ke0ff/IC900_DUClone/3D/stl/IC901F_back2.stl

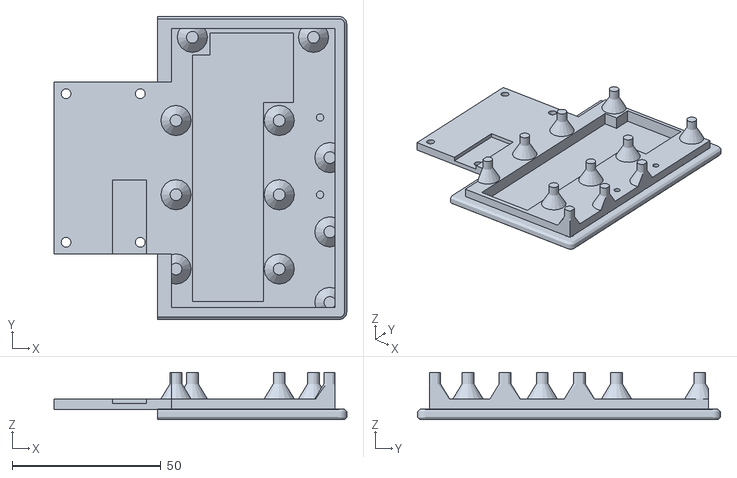
[picture p27: CAD file, 2024-02-04]
3D/stl/IC901F_back2.stl
98.5 x 102.0 x 15.9
