ke0ff/IC900_DUClone/3D/stl/IC901F_sundome.stl

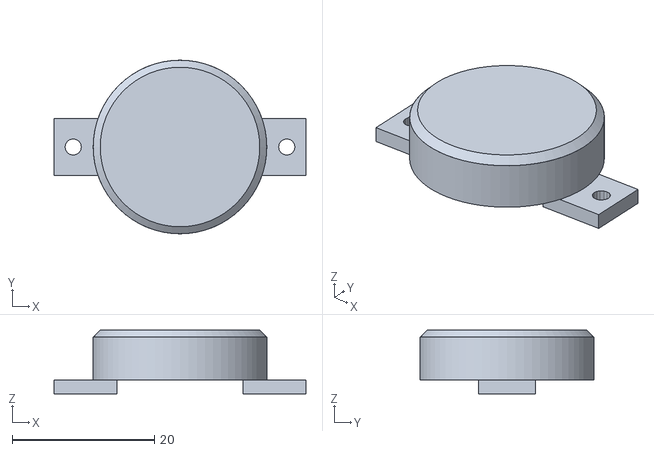
[picture p28: CAD file, 2024-02-04]
3D/stl/IC901F_sundome.stl
35.4 x 24.4 x 8.99
