ke0ff/IC900_DUClone/3D/stl/IC901F_back1.stl

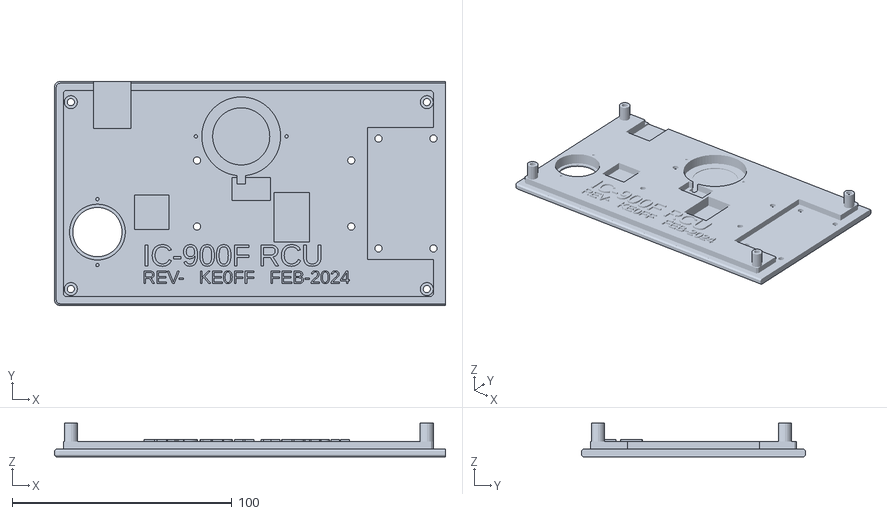
[picture p29: CAD file, 2024-02-04]
3D/stl/IC901F_back1.stl
178.0 x 102.0 x 15.3
