ke0ff/IC900_DUClone/3D/stl/IC901F_dialwin.stl

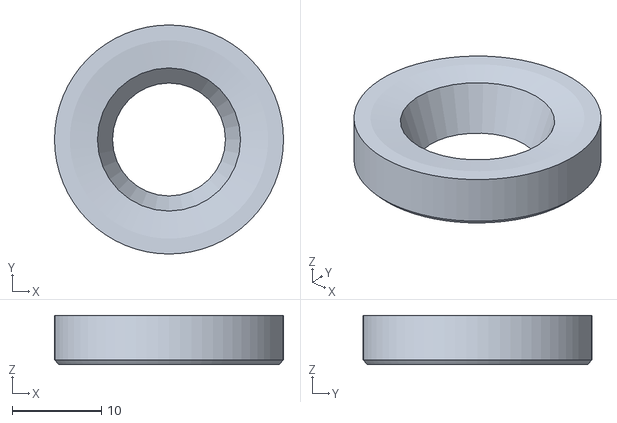
[picture p30: CAD file, 2024-02-04]
3D/stl/IC901F_dialwin.stl
25.7 x 25.7 x 5.50
