ke0ff/IC900_DUClone/3D/stl/IC901F_pot.stl

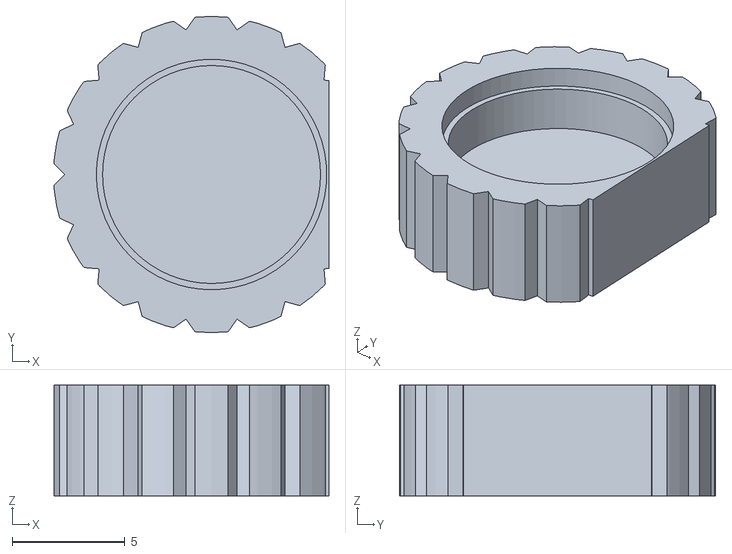
[picture p31: CAD file, 2024-02-04]
3D/stl/IC901F_pot.stl
12.2 x 14.0 x 4.90
