ke0ff/IC900_DUClone/3D/stl/IC900F_vqcap.stl

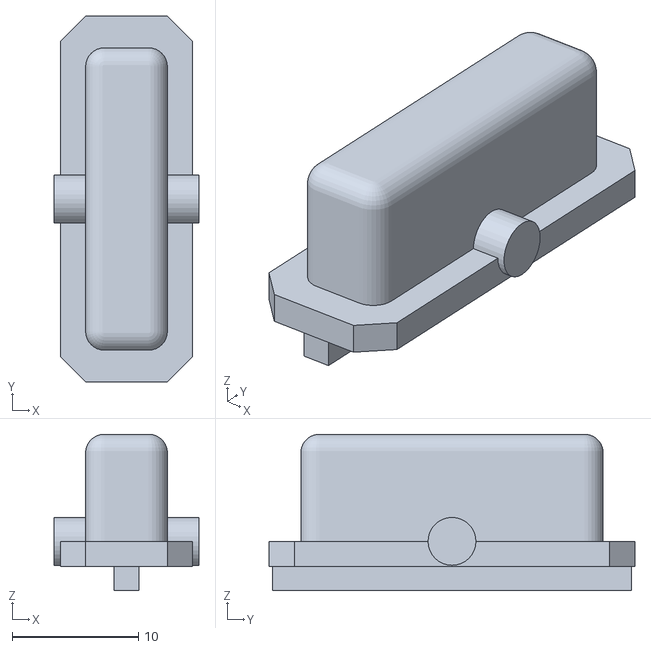
[picture p32: CAD file, 2024-01-06]
3D/stl/IC900F_vqcap.stl
11.5 x 29.0 x 12.4
