ke0ff/IC900_DUClone/3D/stl/LCDpcb.stl

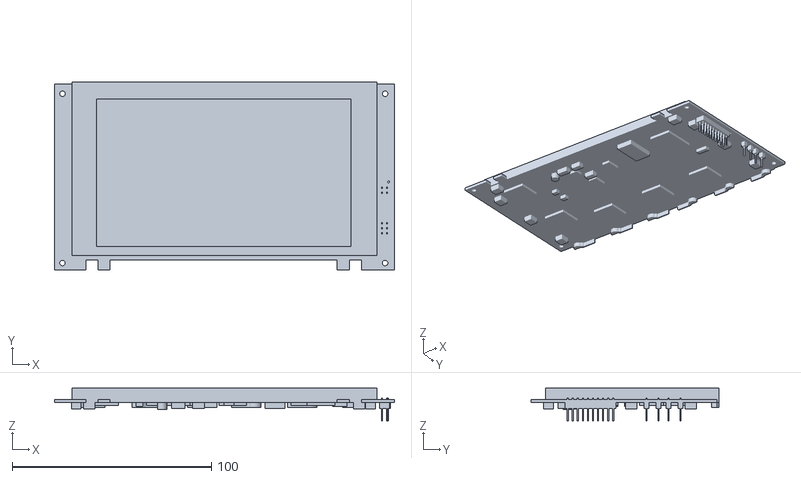
[picture p33: CAD file, 2024-01-06]
3D/stl/LCDpcb.stl
170.5 x 94.5 x 16.4
