ke0ff/IC900_DUClone/3D/stl/IC900F_spacer.stl

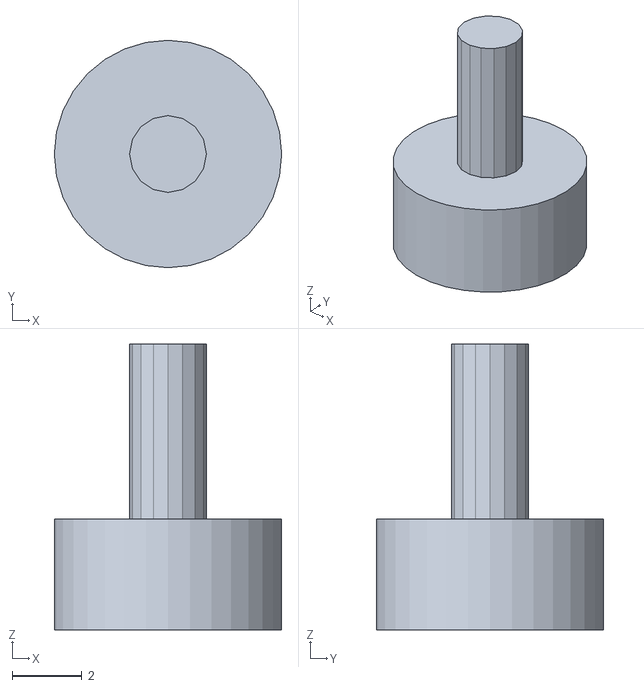
[picture p34: CAD file, 2024-01-06]
3D/stl/IC900F_spacer.stl
6.50 x 6.50 x 8.18
