ke0ff/IC900_DUClone/3D/stl/IC900F_pcb.stl

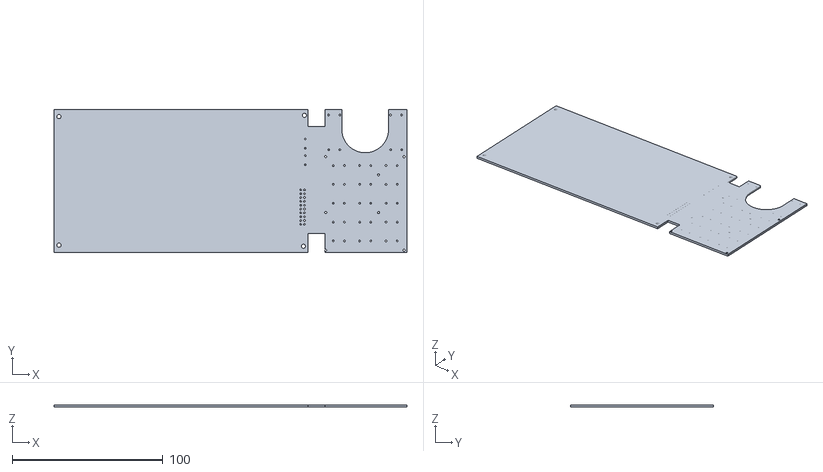
[picture p36: CAD file, 2024-01-06]
3D/stl/IC900F_pcb.stl
234.0 x 94.5 x 1.60
