ke0ff/IC900_DUClone/3D/stl/IC900F_bcap.stl

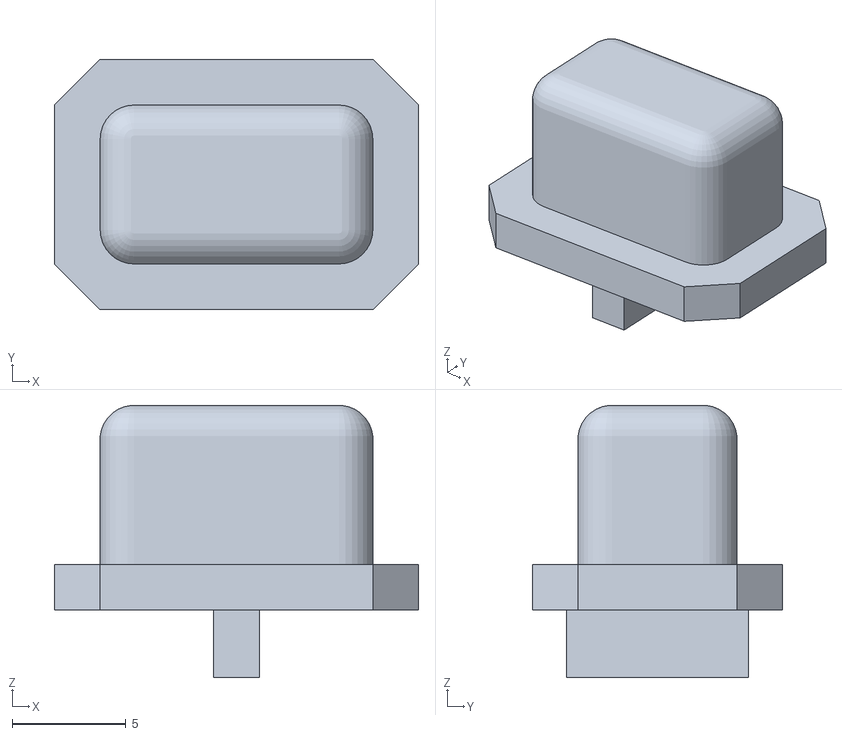
[picture p37: CAD file, 2024-01-06]
3D/stl/IC900F_bcap.stl
16.0 x 11.0 x 12.0
