ke0ff/IC900_DUClone/3D/stl/button.stl

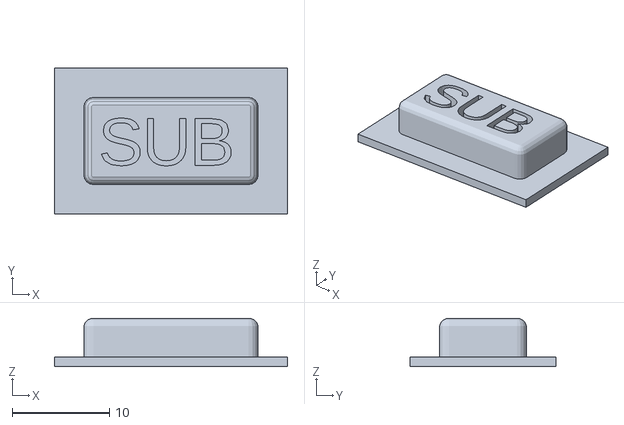
[picture p38: CAD file, 2024-01-06]
3D/stl/button.stl
24.0 x 15.0 x 4.97
