ke0ff/IC900_DUClone/3D/stl/IC900F_side3.stl

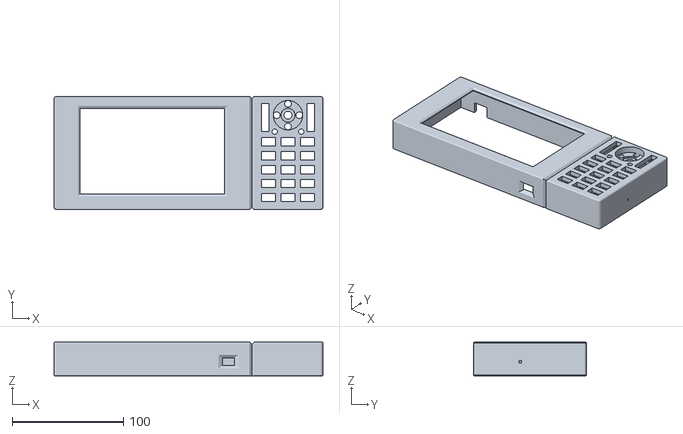
[picture p39: CAD file, 2024-01-06]
3D/stl/IC900F_side3.stl
242.0 x 102.0 x 30.5
