ke0ff/IC900_DUClone/SW/graphics.c

/****************************************************************************************
 ****************** COPYRIGHT (c) 2023 by Joseph Haas (DBA FF Systems)  *****************
 *
 *  File name: graphics.c
 *
 *  Module:    Control
 *
 *  Summary:   graphic symbols for IC900
 *
 *  File scope revision history:
 *    11-24-26 jmh:  creation date
 *
 ***************************************************************************************/
#define	GRAPHINCL

#include "typedef.h"
#include "lcd_db.h"
#include "graphics.h"

U8	gtone[TONESYM_Y][TONESYM_X] = {
		{0x7F,0xFF,0xE0},
		{0x80,0x00,0x10},
		{0xB9,0x25,0xD0},
		{0x92,0xB5,0x10},
		{0x92,0xAd,0x90},
		{0x92,0xA5,0x10},
		{0x91,0x25,0xD0},
		{0x80,0x00,0x10},
		{0x7F,0xFF,0xE0}
};

U8	gdup[DUPSYM_Y][DUPSYM_X] = {
		{ 0x7F , 0xFC , 0x00},
		{ 0x80 , 0x02 , 0x00},
		{ 0xB2 , 0xBA , 0x00},
		{ 0xAA , 0xAA , 0x00},
		{ 0xAA , 0xBA , 0x00},
		{ 0xAA , 0xA2 , 0x00},
		{ 0xB3 , 0xA2 , 0x00},
		{ 0x80 , 0x02 , 0x00},
		{ 0x7F , 0xFC , 0x00}
};

U8	gmem[MEMSYM_Y][MEMSYM_X] = {
		{ 0xC0 , 0x80},
		{ 0xC1 , 0x80},
		{ 0xC1 , 0x80},
		{ 0xE3 , 0x80},
		{ 0xE3 , 0x80},
		{ 0xD5 , 0x80},
		{ 0xD5 , 0x80},
		{ 0xC9 , 0x80},
		{ 0xC9 , 0x80},
		{ 0xC1 , 0x80},
		{ 0xC1 , 0x80}
};

U8	gskp[SKPSYM_Y][SKPSYM_X] = {
		{ 0x7F , 0x00},
		{ 0x80 , 0x80},
		{ 0x9C , 0x80},
		{ 0xA2 , 0x80},
		{ 0xA0 , 0x80},
		{ 0x9C , 0x80},
		{ 0x82 , 0x80},
		{ 0xA2 , 0x80},
		{ 0x9C , 0x80},
		{ 0x80 , 0x80},
		{ 0x7F , 0x00}
};

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
		{ 0x40 , 0x1C , 0x42 , 0x50 , 0xA1 , 0xC0 , 0x10},
		{ 0x40 , 0x18 , 0x42 , 0x52 , 0x90 , 0xC0 , 0x10},
		{ 0x40 , 0x10 , 0x79 , 0x8C , 0x90 , 0x40 , 0x10},
		{ 0x40 , 0x00 , 0x00 , 0x00 , 0x00 , 0x00 , 0x10},
		{ 0x3F , 0xFF , 0xFF , 0xFF , 0xFF , 0xFF , 0xE0}
};
