ke0ff/IC900_DUClone/SW/segments.c

/****************************************************************************************
 ****************** COPYRIGHT (c) 2023 by Joseph Haas (DBA FF Systems)  *****************
 *
 *  File name: segments.c
 *
 *  Module:    Control
 *
 *  Summary:   This is the main code file for the ADF4351 PLL setup application
 *
 *  File scope revision history:
 *    11-24-23 jmh:  creation date
 *
 ***************************************************************************************/
#define	SEGINCL

#include "typedef.h"
#include "lcd_db.h"
#include "segments.h"

/////////////////////////////////////////////////////////////////////////////////////////
/////////////////////////////////////////////////////////////////////////////////////////

//////////////////////////////////
//		 DIGITS - MAIN          // ***************************************************
//////////////////////////////////

U8 digit0[38][3] = {
	{0x01,0xFF,0xF8}, {0x03,0xFF,0xFC}, {0x05,0xFF,0xFA}, {0x0E,0xFF,0xF7},
	{0x0F,0x7F,0xEF}, {0x0F,0x80,0x1F}, {0x0F,0x80,0x1F}, {0x0F,0x80,0x1F},
	{0x0F,0x80,0x1F}, {0x0F,0x80,0x1F}, {0x0F,0x80,0x1F}, {0x0F,0x80,0x1F},
	{0x0F,0x80,0x1F}, {0x0F,0x80,0x1F}, {0x0F,0x80,0x1F}, {0x0F,0x00,0x0F},
	{0x0E,0x00,0x07}, {0x04,0x00,0x02}, {0x00,0x00,0x00}, {0x04,0x00,0x02},
	{0x0E,0x00,0x07}, {0x0F,0x00,0x0F}, {0x0F,0x80,0x1F}, {0x0F,0x80,0x1F},
	{0x0F,0x80,0x1F}, {0x0F,0x80,0x1F}, {0x0F,0x80,0x1F}, {0x0F,0x80,0x1F},
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
		{0x01,0xF8}
};

U8 segs_e[12] = {
		 0x04,0x0E,0x0E,0x0E,
		 0x0E,0x0E,0x0E,0x0E,
		 0x0E,0x04,0x00,0x00};

U8 segs_f[12] = {
		 0x00,0x00,0x04,0x0E,
		 0x0E,0x0E,0x0E,0x0E,
		 0x0E,0x0E,0x0E,0x04};

U8 segs_g[3][2] = {
		{0x01,0xF8},
		{0x03,0xFC},
		{0x01,0xF8}
};

U8 segs_p[2] = {0x60,0x60};
